zhmakin/PS800_Takeover/Ver 2/Parts/FETs/APG095N01K.pdf

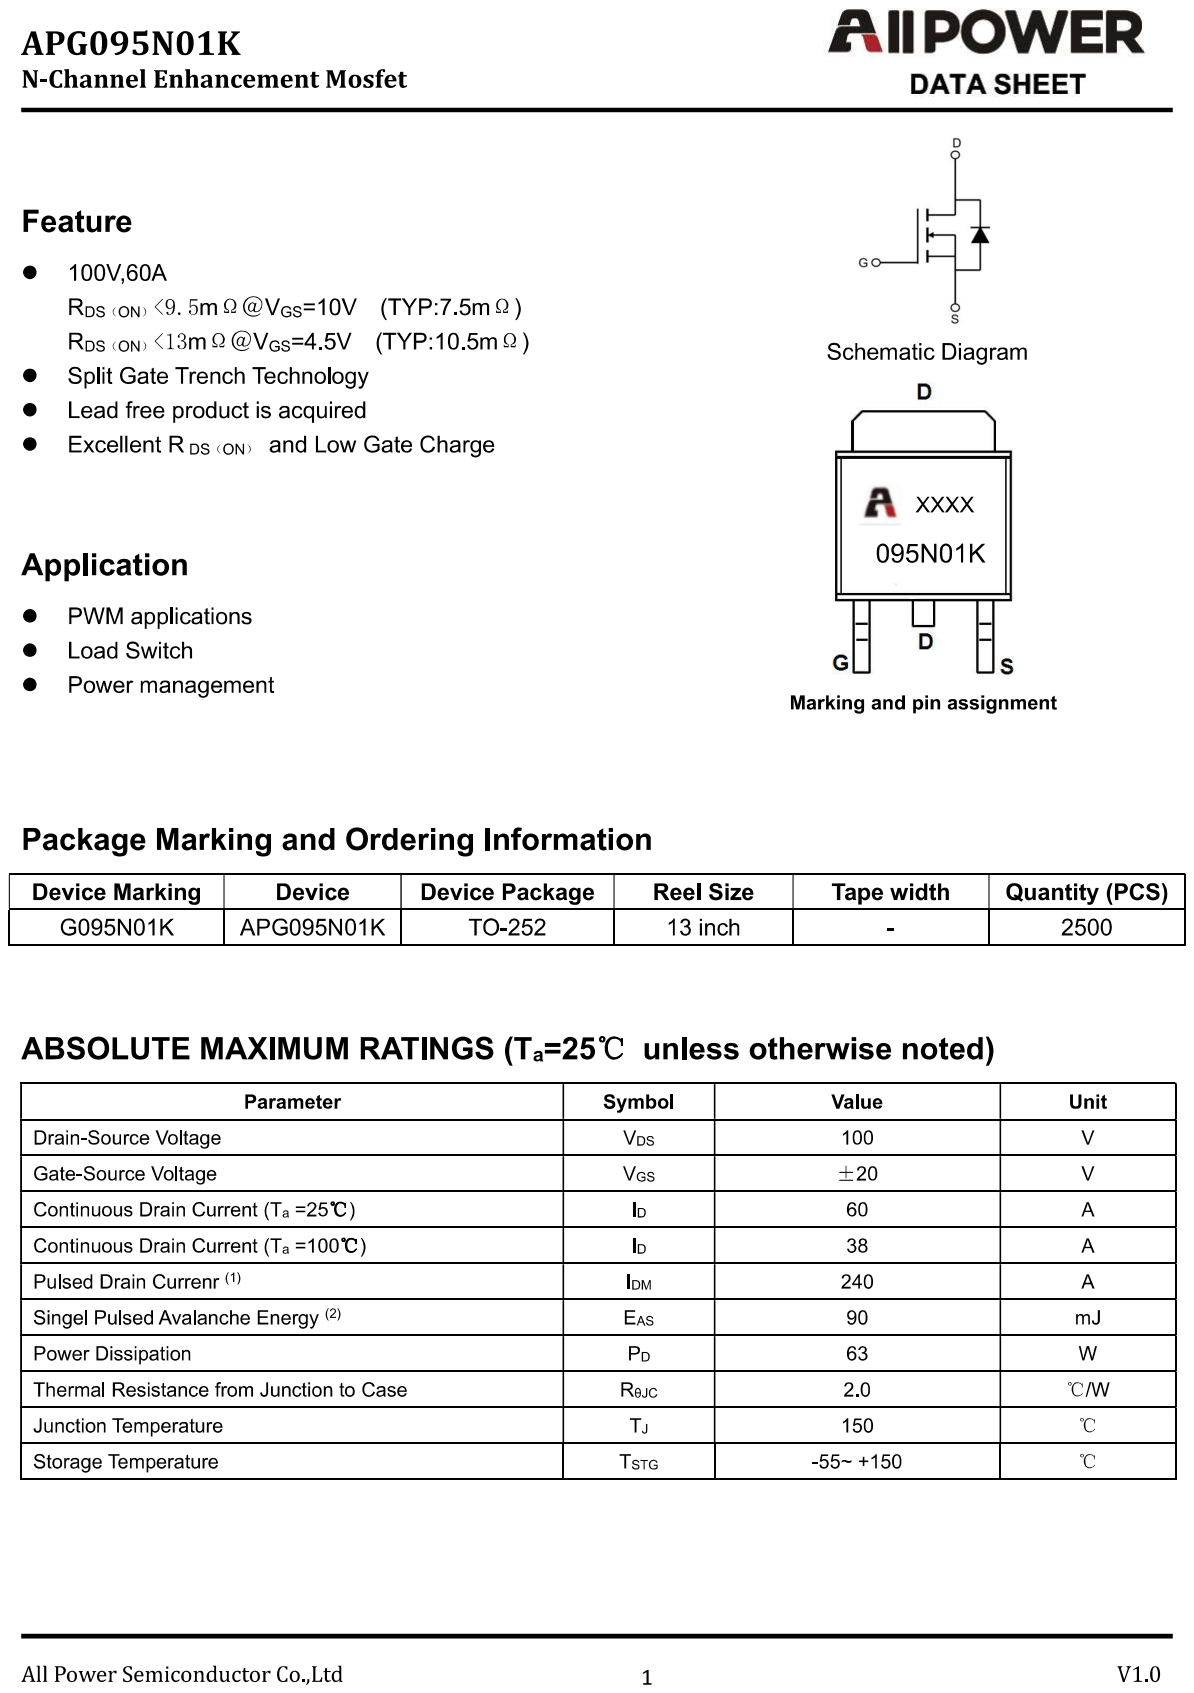
[picture p13: page 1]
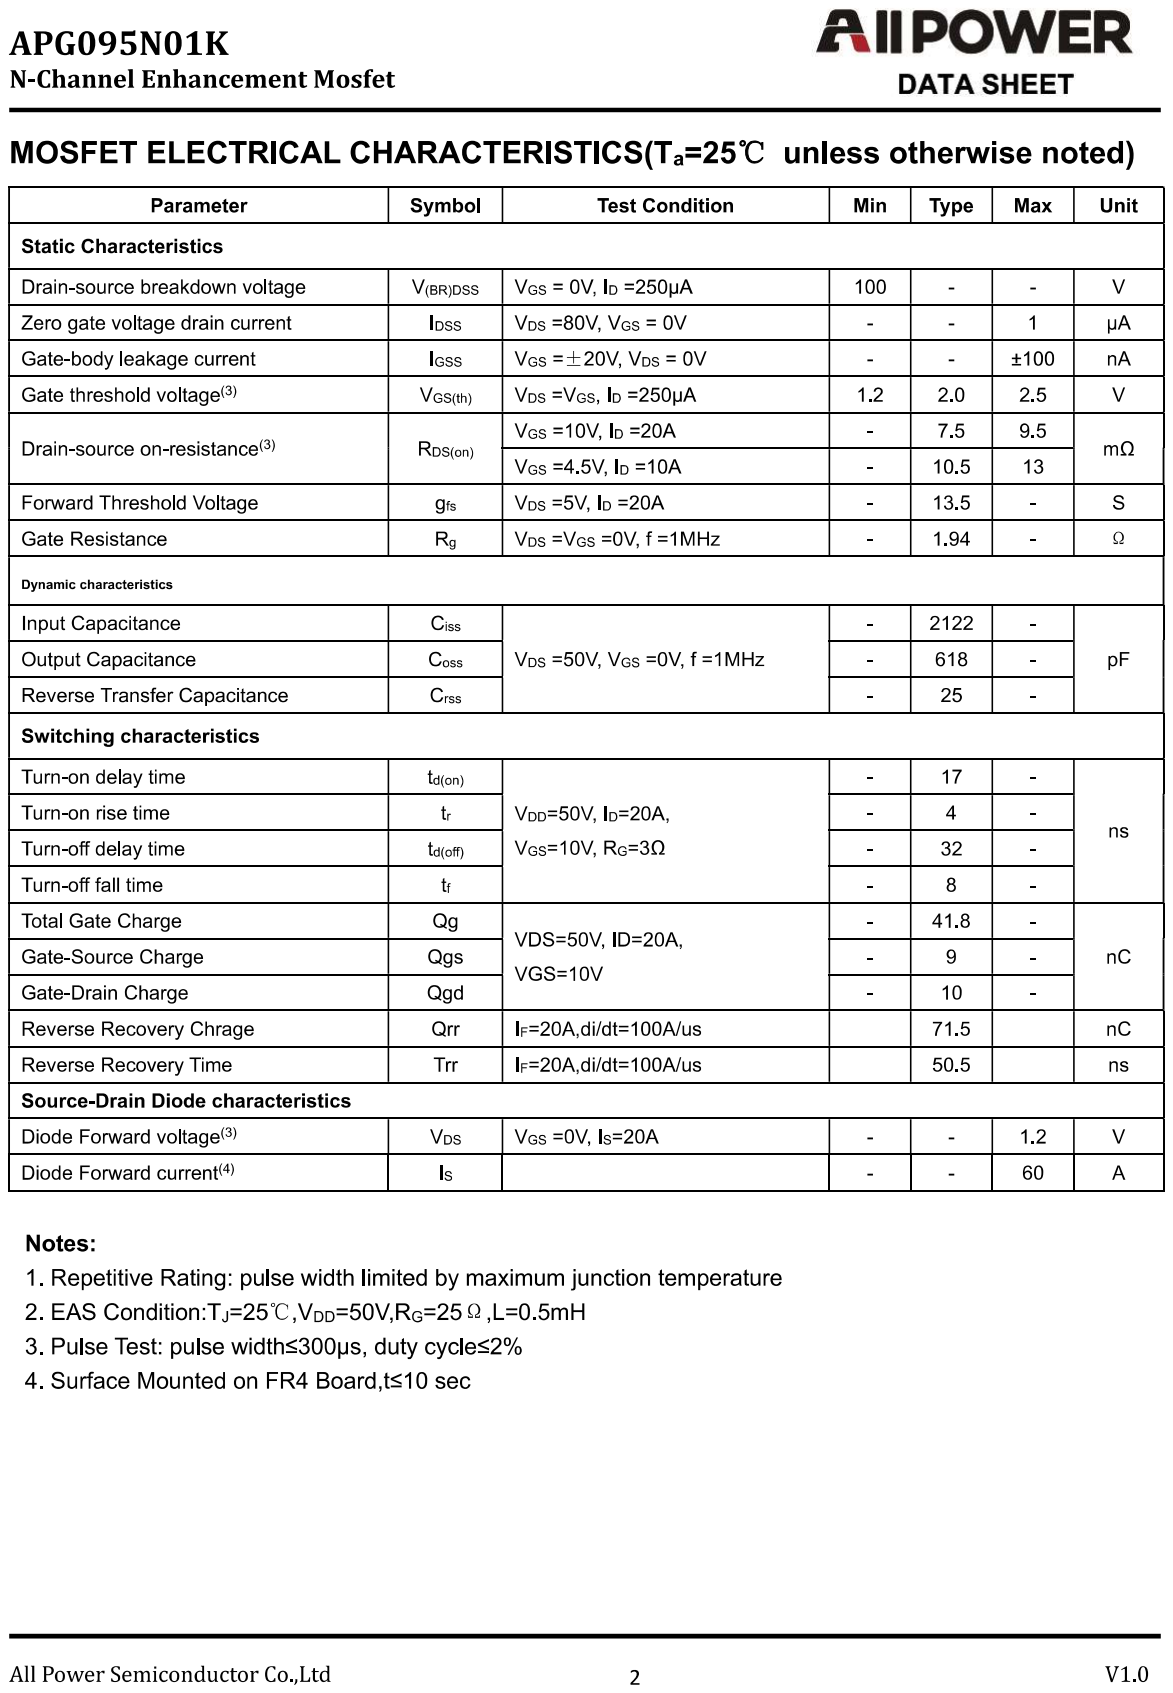
[picture p14: page 2]
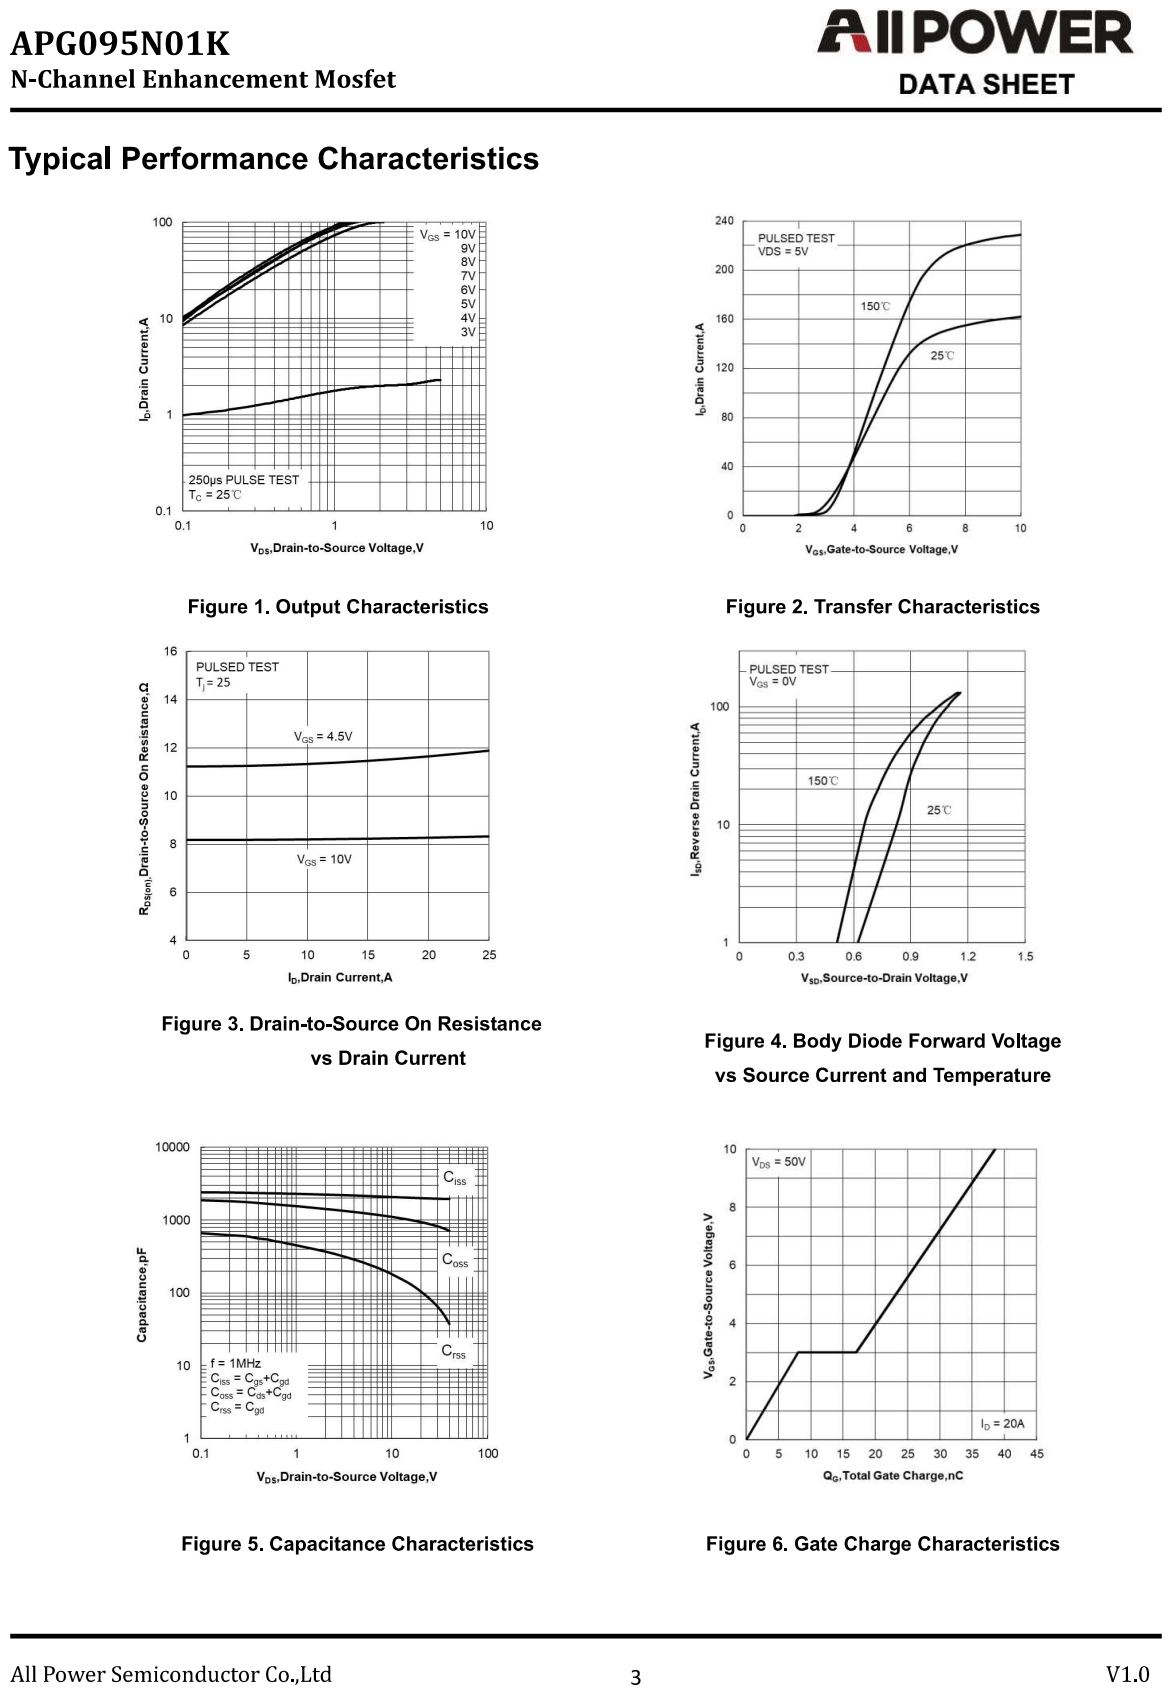
[picture p15: page 3]
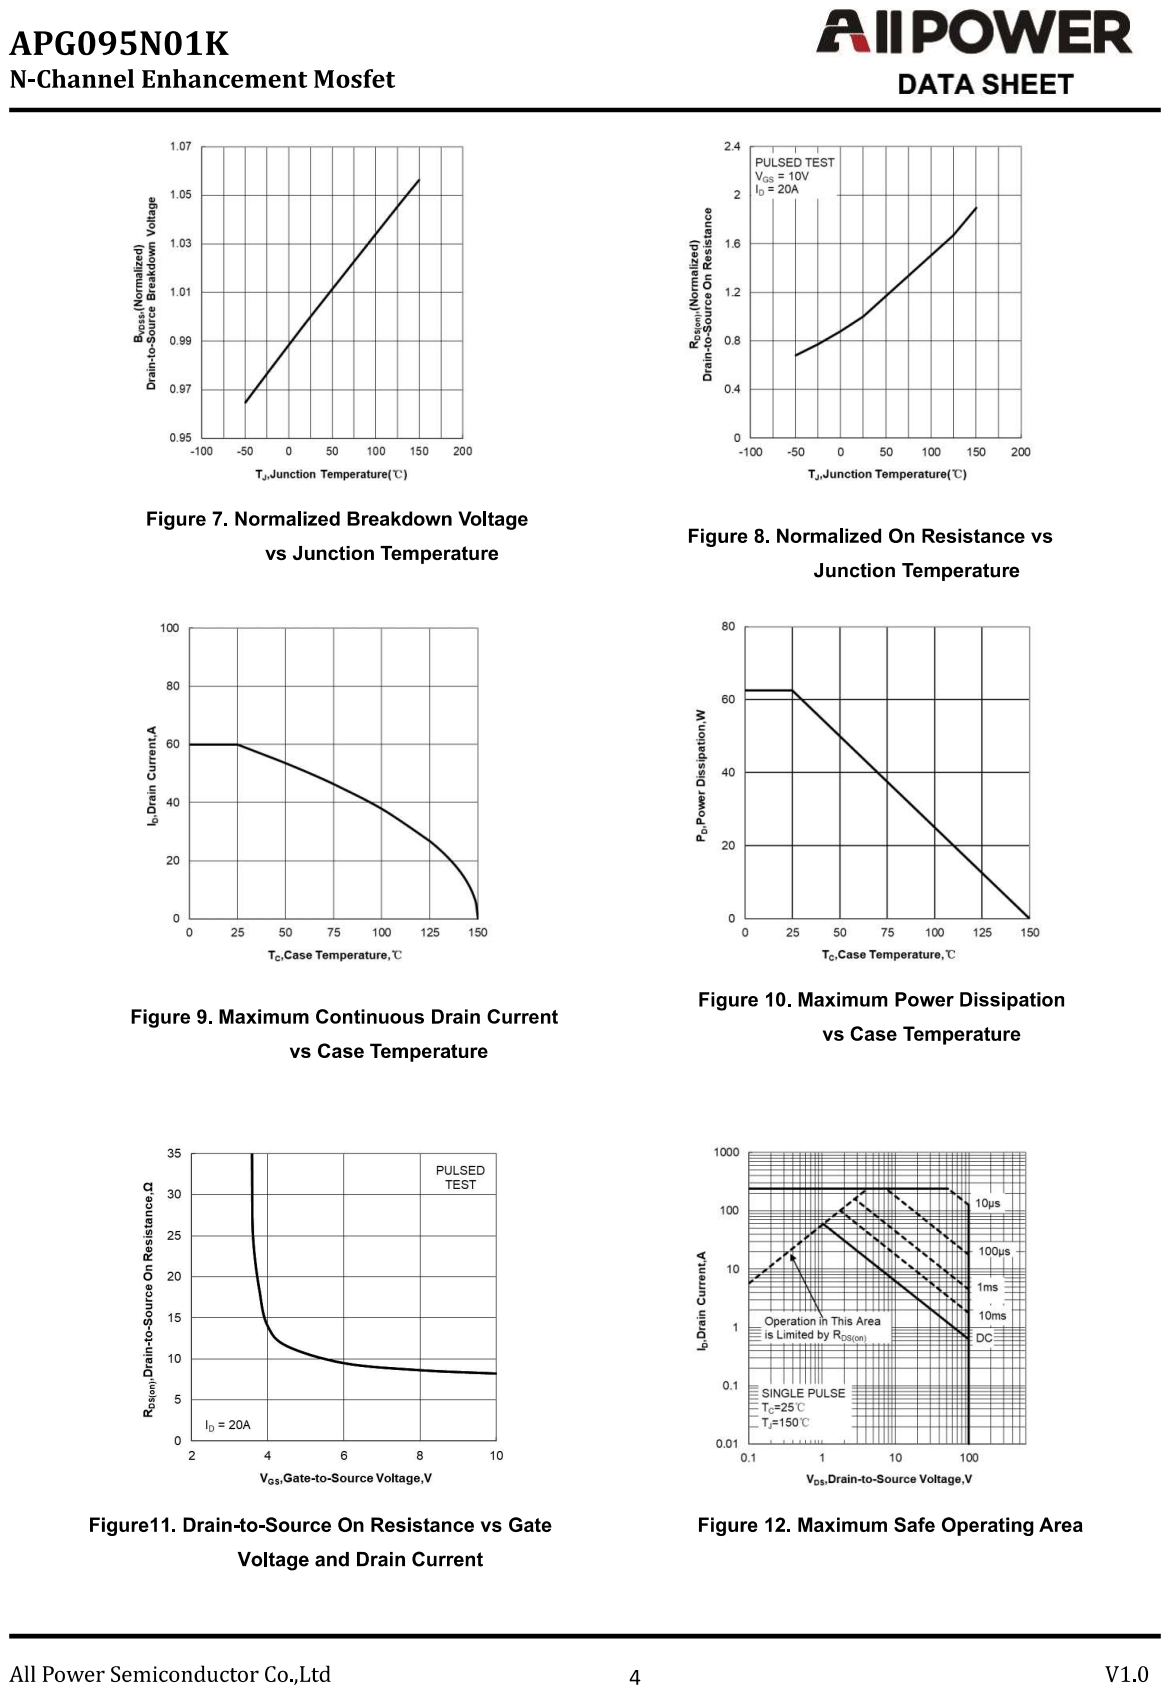
[picture p16: page 4]
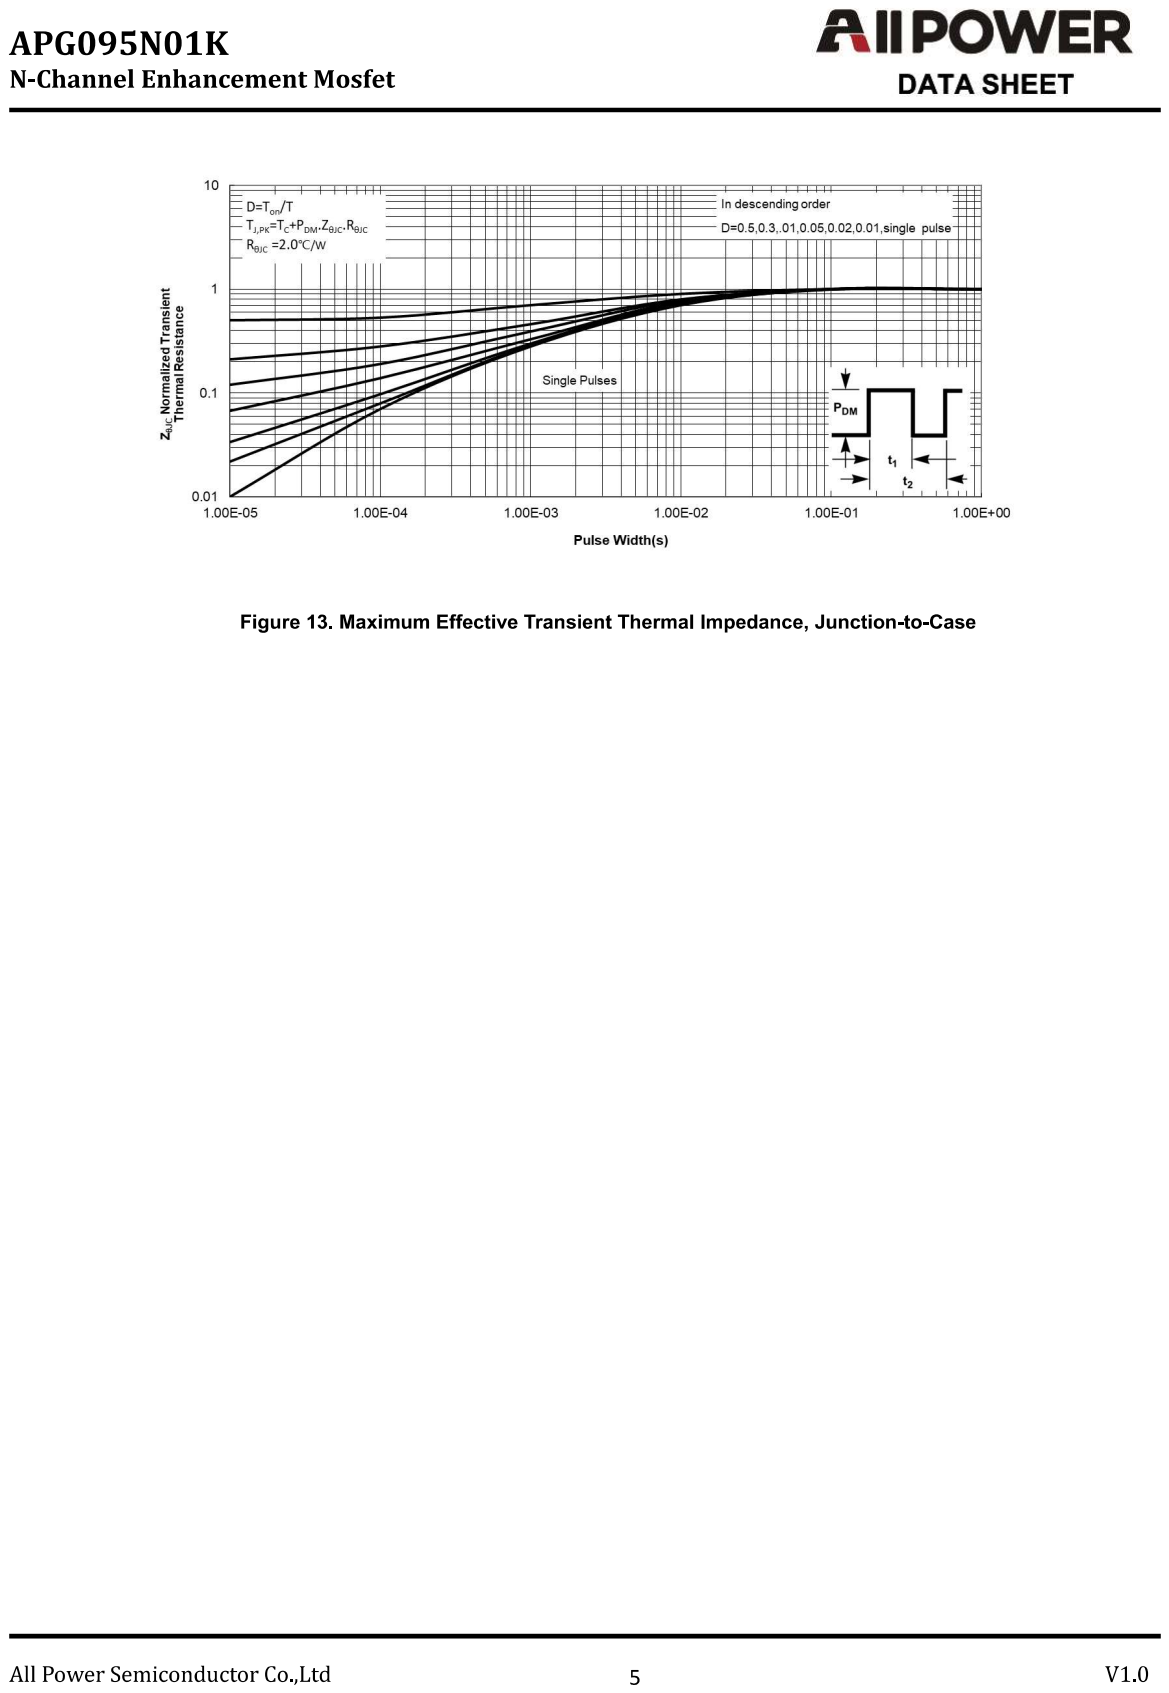
[picture p17: page 5]
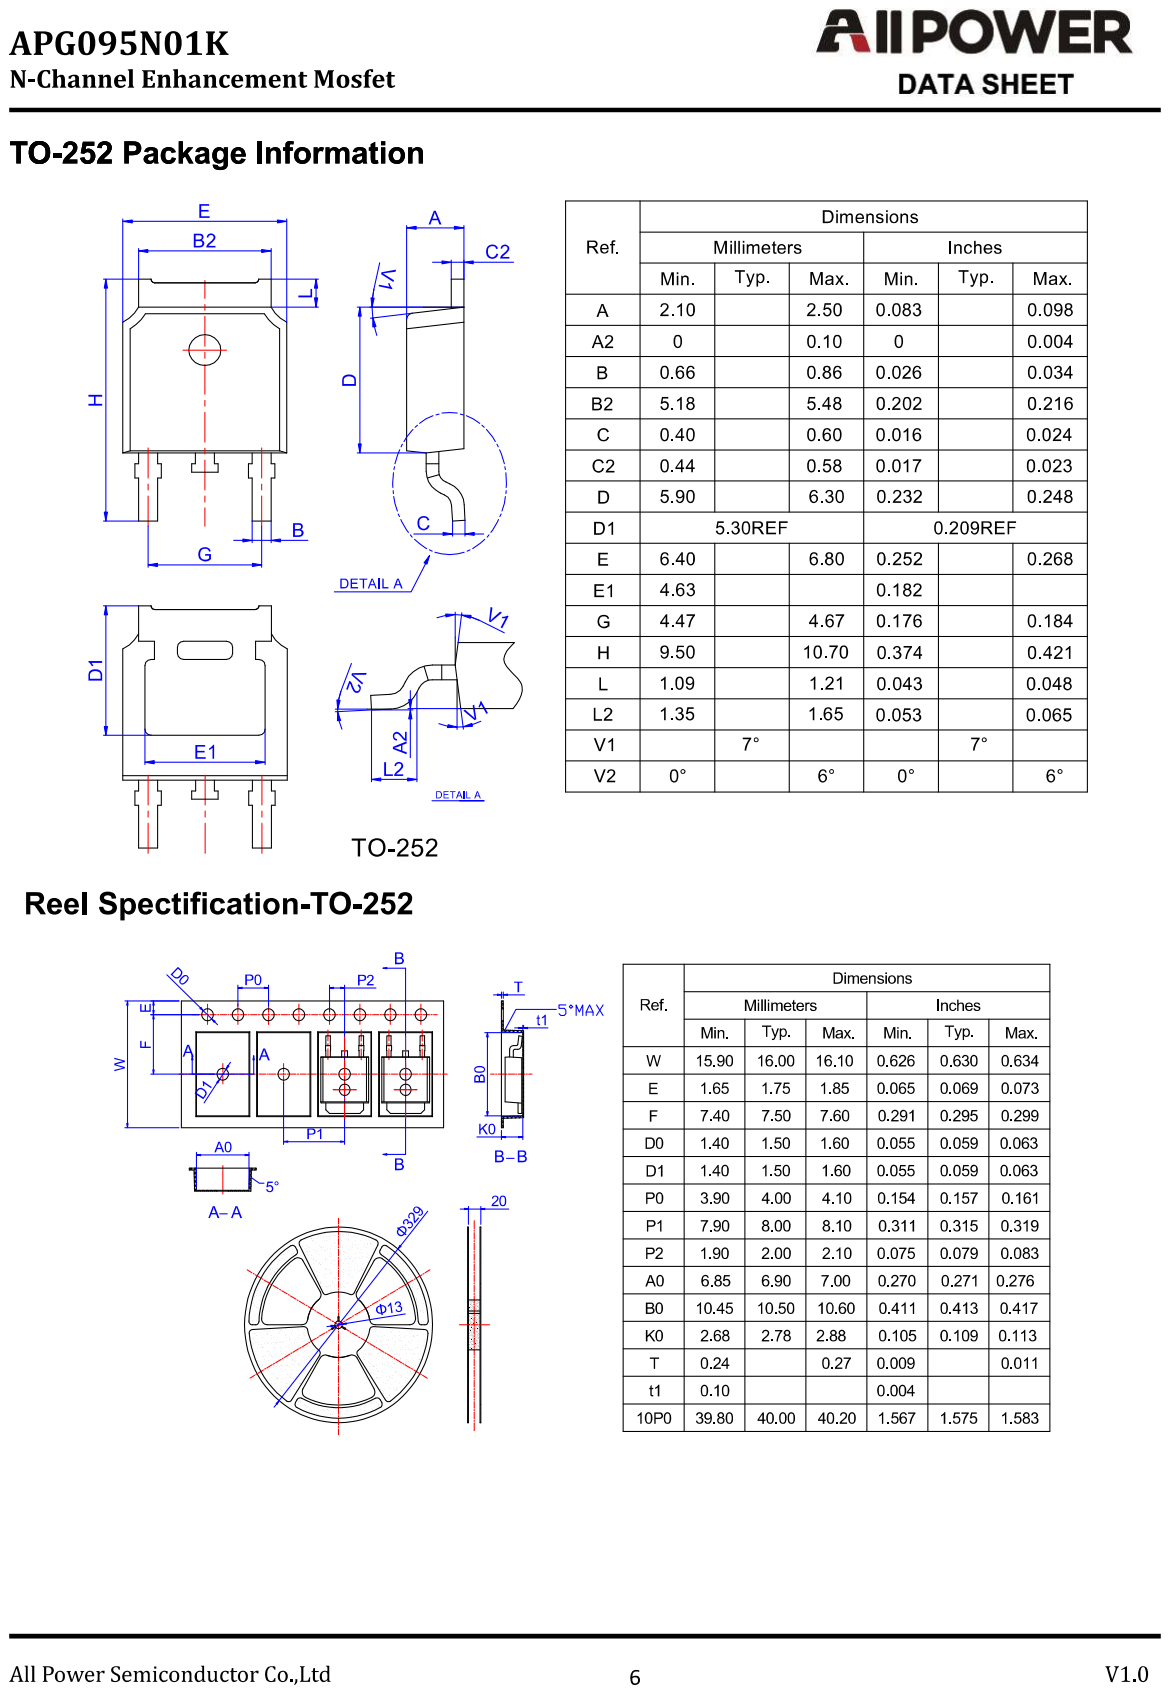
[picture p18: page 6]
